SirLefti/piboy/docs/piboy.jpg

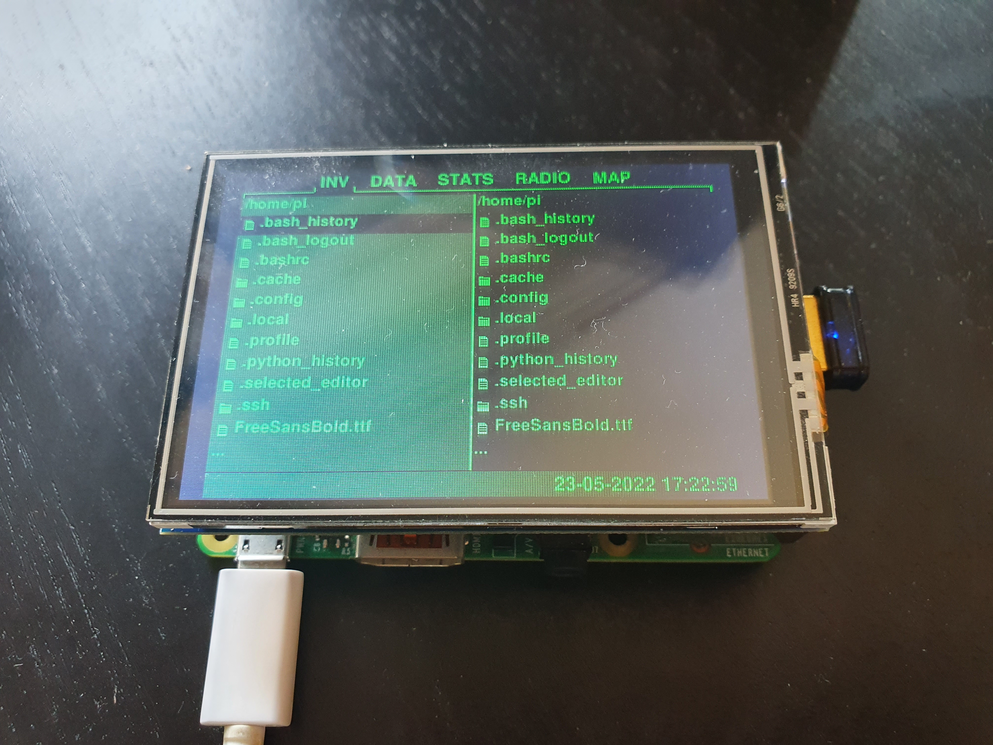
docs/piboy.jpg
