SirLefti/piboy/app/MapApp.py

import math
from typing import Any, Callable, Generator, Optional, Union

from injector import inject
from PIL import Image, ImageDraw, ImageOps

from app.App import SelfUpdatingApp
from core import resources
from core.decorator import override
from data.LocationProvider import Location, LocationException, LocationProvider
from data.TileProvider import TileProvider
from environment import AppConfig


class MapApp(SelfUpdatingApp):
    __SCROLL_FACTOR = 10
    __CONTROL_SIZE = 30
    __CONTROL_PADDING = 4

    class Control:
        """
        Represents a UI control element. A control has a texture, initial selection state, various callbacks and a flag
        that indicates, if it is an instant action. Instant actions will not get the SELECTED state when selected and
        thus cannot use callbacks the directional callbacks (up, right, down, left).
        """

        # not an enum, because we have to reassign the values
        class SelectionState:
            """
            Container class representing a state of a control element. A selection state has an element color and
            a background color.
            Initially, the state members are all none, replace them before usage or create new ones for a specific use.
            """

            # skip first argument, it is the value for the enum
            def __init__(self, color: tuple[int, int, int], background_color: tuple[int, int, int]):
                self.__color = color
                self.__background_color = background_color

            @property
            def color(self) -> tuple[int, int, int]:
                return self.__color

            @property
            def background_color(self) -> tuple[int, int, int]:
                return self.__background_color

        NONE: SelectionState
        FOCUSED: SelectionState
        SELECTED: SelectionState

        def __init__(self, icon_bitmap: Image.Image, initial_state: SelectionState,
                     on_select: Optional[Callable[[], None]] = None, on_deselect: Optional[Callable[[], None]] = None,
                     on_key_left: Optional[Callable[[], None]] = None,
                     on_key_right: Optional[Callable[[], None]] = None,
                     on_key_up: Optional[Callable[[], None]] = None, on_key_down: Optional[Callable[[], None]] = None,
                     instant_action=False):
            self.__icon_bitmap = icon_bitmap
            self.__on_select = on_select
            self.__on_deselect = on_deselect
            self.__on_key_left = on_key_left
            self.__on_key_right = on_key_right
            self.__on_key_up = on_key_up
            self.__on_key_down = on_key_down
            self.__instant_action = instant_action  # instant actions won't get the SELECTED flag
            self.__selection_state = initial_state

        def on_key_left(self):
            if self.__on_key_left is not None:
                self.__on_key_left()

        def on_key_right(self):
            if self.__on_key_right is not None:
                self.__on_key_right()

        def on_key_up(self):
            if self.__on_key_up is not None:
                self.__on_key_up()

        def on_key_down(self):
            if self.__on_key_down is not None:
                self.__on_key_down()

        def on_select(self):
            """When pressing button A"""
            if not self.__instant_action:
                self.__selection_state = self.SELECTED
            if self.__on_select is not None:
                self.__on_select()

        def on_deselect(self):
            """When pressing button B"""
            if not self.__instant_action:
                self.__selection_state = self.FOCUSED
            if self.__on_deselect is not None:
                self.__on_deselect()

        def on_focus(self):
            """When moving focus on this control"""
            self.__selection_state = self.FOCUSED

        def on_blur(self):
            """When moving focus away from this control"""
            self.__selection_state = self.NONE

        def draw(self, draw: ImageDraw.ImageDraw, left_top: tuple[int, int]):
            width, height = self.__icon_bitmap.size
            left, top = left_top
            draw.rectangle(left_top + (left + width - 1, top + height - 1),
                           fill=self.__selection_state.background_color)
            draw.bitmap(left_top, self.__icon_bitmap, fill=self.__selection_state.color)

        def is_selected(self) -> bool:
            return self.__selection_state == self.SELECTED

    @inject
    def __init__(self, draw_callback: Callable[[bool], None],
                 location_provider: LocationProvider, tile_provider: TileProvider, app_config: AppConfig):
        super().__init__(self.__update_location)
        self.__app_size = app_config.app_size
        self.__background = app_config.background
        self.__color = app_config.accent
        self.__color_dark = app_config.accent_dark
        self.__font = app_config.font_standard

        # init selection states
        self.Control.NONE = self.Control.SelectionState(self.__color_dark, self.__background)
        self.Control.FOCUSED = self.Control.SelectionState(self.__color, self.__background)
        self.Control.SELECTED = self.Control.SelectionState(self.__background, self.__color)

        self.__draw_callback = draw_callback
        self.__draw_callback_kwargs = {'partial': True}
        self.__location_provider = location_provider
        self.__tile_provider = tile_provider
        self.__zoom = 15
        self.__x_offset = 0
        self.__y_offset = 0
        self.__position: Union[Location, None] = None
        try:
            self.__position = self.__location_provider.get_location()
            self.__connection_lost = False
        except LocationException:
            self.__connection_lost = True

        def zoom_in():
            if self.__zoom + 1 in self.__tile_provider.zoom_range:
                self.__zoom = self.__zoom + 1

        def zoom_out():
            if self.__zoom - 1 in self.__tile_provider.zoom_range:
                self.__zoom = self.__zoom - 1

        def reset_offset():
            self.__x_offset = 0
            self.__y_offset = 0

        def move_left():
            self.__x_offset -= 1

        def move_right():
            self.__x_offset += 1

        def move_up():
            self.__y_offset -= 1

        def move_down():
            self.__y_offset += 1

        self.__controls: list[MapApp.Control] = [
            self.Control(ImageOps.invert(resources.minus_icon), initial_state=self.Control.NONE,
                         on_select=zoom_out, instant_action=True),
            self.Control(ImageOps.invert(resources.plus_icon), initial_state=self.Control.NONE,
                         on_select=zoom_in, instant_action=True),
            self.Control(ImageOps.invert(resources.move_icon), initial_state=self.Control.NONE,
                         on_key_left=move_left, on_key_right=move_right,
                         on_key_up=move_up, on_key_down=move_down,
                         on_select=self.stop_updating, on_deselect=self.start_updating),
            self.Control(ImageOps.invert(resources.focus_icon), initial_state=self.Control.NONE,
                         on_select=reset_offset, instant_action=True)
        ]
        self.__focused_control_index = 0
        # focus the currently focused control to initially update the selection state
        self.__controls[self.__focused_control_index].on_focus()

    @property
    @override
    def title(self) -> str:
        return 'MAP'

    @property
    @override
    def refresh_time(self) -> float:
        return 2.0

    def __update_location(self):
        if self.__x_offset == 0 and self.__y_offset == 0:
            try:
                self.__position = self.__location_provider.get_location()
                self.__connection_lost = False
            except LocationException:
                self.__connection_lost = True
            self.__draw_callback(**self.__draw_callback_kwargs)

    @override
    def draw(self, image: Image.Image, partial=False) -> Generator[tuple[Image.Image, int, int], Any, None]:
        draw = ImageDraw.Draw(image)
        width, height = self.__app_size
        left_top = (0, 0)
        side_tab_width = 120
        side_tab_padding = 5
        line_height = 20
        font = self.__font

        size = (width - side_tab_width, height)

        lat: Union[float, None] = None
        lon: Union[float, None] = None
        if self.__position is None:
            # if location is not available, just paste a black image for now
            left, top = left_top
            tile_width, tile_height = size
            right_bottom = (left + tile_width, top + tile_height)
            draw.rectangle(left_top + right_bottom, self.__background, self.__color, 3)
        else:
            # if location is available, just fetch the tile as usual
            lat = self.__position.latitude
            lon = self.__position.longitude
            tile = self.__tile_provider.get_tile(lat, lon, self.__zoom, size=size,
                                                 x_offset=self.__x_offset * self.__SCROLL_FACTOR,
                                                 y_offset=self.__y_offset * self.__SCROLL_FACTOR)
            image.paste(tile.image, left_top)

            # Calculate the relative position of the current location on the tile, because the tile is not centered
            # around the given location. It even works with resized and cropped tiles, as long as the center stays the
            # center. Otherwise, calculate the position where a virtual line from the center to the marker would cross
            # the edge to draw a different marker that indicates where the location would be.
            if self.__x_offset * self.__SCROLL_FACTOR + int(size[0] / 2) in range(size[0]) \
                    and self.__y_offset * self.__SCROLL_FACTOR + int(size[1] / 2) in range(size[1]):
                tile_top, tile_left = tile.top_left
                tile_bottom, tile_right = tile.bottom_right
                x_position = (lon - tile_left) / (tile_right - tile_left)
                y_position = (lat - tile_top) / (tile_bottom - tile_top)
                marker_center = (left_top[0] + size[0] * x_position - self.__x_offset * self.__SCROLL_FACTOR,
                                 left_top[1] + size[1] * y_position - self.__y_offset * self.__SCROLL_FACTOR)
                marker_size = 20
                draw.polygon([marker_center,
                              (marker_center[0] - int(marker_size / 2), marker_center[1] - marker_size),
                              (marker_center[0] + int(marker_size / 2), marker_center[1] - marker_size)],
                             fill=self.__color_dark)
            else:
                def draw_outside_marker(edge_position: tuple[int, int], center_position: tuple[int, int]):
                    marker_width = 3
                    marker_length_percentage = .2
                    tip_length_percentage = marker_length_percentage * .75
                    tip_angle = 30
                    diff_x = edge_position[0] - center_position[0]
                    diff_y = edge_position[1] - center_position[1]
                    draw.line((edge_position[0] - diff_x * marker_length_percentage,
                               edge_position[1] - diff_y * marker_length_percentage) +
                              edge_position, fill=self.__color, width=marker_width)  # line towards center

                    def dot(v1: tuple[float, float], v2: tuple[float, float]) -> float:
                        """ vector dot product """
                        return sum([i * j for (i, j) in zip(v1, v2)])

                    def mag(v: tuple[float, float]) -> float:
                        """ vector magnitude/length """
                        return math.sqrt(dot(v, v))

                    v_diff = (diff_x, diff_y)  # line vector with reference point at (0, 0)
                    v_ref = (0, 1)  # vector that goes straight up or down
                    adjust_left = 1 if v_diff[0] > v_ref[0] else -1  # adjust the angle if located left from ref point
                    dot_prod = dot(v_diff, v_ref)
                    mag_diff = mag(v_diff)
                    mag_ref = mag(v_ref)
                    radians = math.acos(dot_prod / (mag_diff * mag_ref))  # calculate angle in radians
                    angle = math.degrees(radians) * adjust_left  # convert to angle and adjust

                    tip_length = mag_diff * tip_length_percentage
                    # add 180 to flip and apply tip angle, convert back to radians
                    tip_1_x = tip_length * math.sin(math.radians(angle + tip_angle + 180))
                    tip_1_y = tip_length * math.cos(math.radians(angle + tip_angle + 180))
                    tip_2_x = tip_length * math.sin(math.radians(angle - tip_angle + 180))
                    tip_2_y = tip_length * math.cos(math.radians(angle - tip_angle + 180))

                    draw.line((edge_position[0] + tip_1_x, edge_position[1] + tip_1_y) +
                              edge_position, fill=self.__color, width=marker_width)  # first tip
                    draw.line((edge_position[0] + tip_2_x, edge_position[1] + tip_2_y) +
                              edge_position, fill=self.__color, width=marker_width)  # second tip

                # exclude cases where x_offset or y_offset are zero, division is not possible, but marker is straight
                # anyway
                map_center = (left_top[0] + size[0] // 2, left_top[1] + size[1] // 2)
                if self.__x_offset == 0:
                    if self.__y_offset > 0:
                        edge_center = (left_top[0] + size[0] // 2, left_top[1])
                        draw_outside_marker(edge_center, map_center)
                    else:
                        edge_center = (left_top[0] + size[0] // 2, left_top[1] + size[1])
                        draw_outside_marker(edge_center, map_center)
                elif self.__y_offset == 0:
                    if self.__x_offset > 0:
                        edge_center = (left_top[0], left_top[1] + size[1] // 2)
                        draw_outside_marker(edge_center, map_center)
                    else:
                        edge_center = (left_top[0] + size[0], left_top[1] + size[1] // 2)
                        draw_outside_marker(edge_center, map_center)
                else:
                    # neither x nor y are zero, division possible
                    # positive ratio means top-left or bottom-right sector, negativ means others
                    vertical_limit = size[0] / size[1]  # x / y
                    horizontal_limit = size[1] / size[0]  # y / x
                    vertical_ratio = self.__x_offset / self.__y_offset
                    horizontal_ratio = self.__y_offset / self.__x_offset
                    # calculate edge_center by taking the center of the edge and adding or subtracting the product of
                    # the other edge's half-length and the ratio
                    if -vertical_limit <= vertical_ratio <= vertical_limit:
                        if self.__y_offset > 0:
                            edge_center = (int(left_top[0] + size[0] // 2 - (size[1] // 2) * vertical_ratio),
                                           left_top[1])
                            draw_outside_marker(edge_center, map_center)
                        else:
                            edge_center = (int(left_top[0] + size[0] // 2 + (size[1] // 2) * vertical_ratio),
                                           left_top[1] + size[1])
                            draw_outside_marker(edge_center, map_center)
                    elif -horizontal_limit <= horizontal_ratio <= horizontal_limit:
                        if self.__x_offset > 0:
                            edge_center = (left_top[0],
                                           int(left_top[1] + size[1] // 2 - (size[0] // 2) * horizontal_ratio))
                            draw_outside_marker(edge_center, map_center)
                        else:
                            edge_center = (left_top[0] + size[0],
                                           int(left_top[1] + size[1] // 2 + (size[0] // 2) * horizontal_ratio))
                            draw_outside_marker(edge_center, map_center)

        # draw location info
        cursor = (left_top[0] + size[0] + side_tab_padding, left_top[1])
        draw.text(cursor, 'lat: unknown' if lat is None else 'lat: {:.4f}°'.format(lat), self.__color, font=font)
        cursor = (cursor[0], cursor[1] + line_height)
        draw.text(cursor, 'lon: unknown' if lon is None else 'lon: {:.4f}°'.format(lon), self.__color, font=font)
        cursor = (cursor[0], cursor[1] + line_height)
        draw.text(cursor, f'zoom: {self.__zoom}x', self.__color, font=font)
        if self.__x_offset != 0 or self.__y_offset != 0:
            cursor = (cursor[0], cursor[1] + line_height)
            draw.text(cursor, f'x: {self.__x_offset}, y: {self.__y_offset}', self.__color, font=font)
        if self.__connection_lost:
            cursor = (cursor[0], cursor[1] + line_height)
            draw.text(cursor, f'connection lost', self.__color, font=font)

        # draw controls
        cursor = (left_top[0] + size[0] - self.__CONTROL_SIZE - self.__CONTROL_PADDING,
                  left_top[1] + size[1] - self.__CONTROL_SIZE - self.__CONTROL_PADDING)
        for control in self.__controls:
            control.draw(draw, cursor)
            cursor = (cursor[0], cursor[1] - self.__CONTROL_SIZE - 2 * self.__CONTROL_PADDING)

        if partial:
            right_bottom = width, height
            yield image.crop(left_top + right_bottom), *left_top  # noqa (unpacking type check fail)
        else:
            yield image, 0, 0

    @override
    def on_key_left(self):
        if self.__controls[self.__focused_control_index].is_selected():
            self.__controls[self.__focused_control_index].on_key_left()

    @override
    def on_key_right(self):
        if self.__controls[self.__focused_control_index].is_selected():
            self.__controls[self.__focused_control_index].on_key_right()

    @override
    def on_key_up(self):
        if self.__controls[self.__focused_control_index].is_selected():
            self.__controls[self.__focused_control_index].on_key_up()
        else:
            self.__controls[self.__focused_control_index].on_blur()
            self.__focused_control_index = min(self.__focused_control_index + 1, len(self.__controls) - 1)
            self.__controls[self.__focused_control_index].on_focus()

    @override
    def on_key_down(self):
        if self.__controls[self.__focused_control_index].is_selected():
            self.__controls[self.__focused_control_index].on_key_down()
        else:
            self.__controls[self.__focused_control_index].on_blur()
            self.__focused_control_index = max(self.__focused_control_index - 1, 0)
            self.__controls[self.__focused_control_index].on_focus()

    @override
    def on_key_a(self):
        self.__controls[self.__focused_control_index].on_select()

    @override
    def on_key_b(self):
        self.__controls[self.__focused_control_index].on_deselect()
