SirLefti/piboy/app/UpdateApp.py

import logging
import re
import sys
import threading
from subprocess import CompletedProcess, run
from typing import Any, Callable, Collection, Generator, Optional

from injector import inject
from PIL import Image, ImageDraw

from app.App import App
from core.decorator import override
from environment import AppConfig

# type aliases
ActionCallable = Callable[[], CompletedProcess[str]]
ResultTextCallable = Callable[[CompletedProcess[str]], str]
ContinueCallable = Callable[[CompletedProcess[str]], bool]
ActionDefinition = tuple[ActionCallable, ResultTextCallable] | tuple[ActionCallable, ResultTextCallable, ContinueCallable]

logger = logging.getLogger('app')

class UpdateApp(App):
    LINE_HEIGHT = 20
    CENTER_OFFSET = 10

    class Option:

        def __init__(self, name: str, *actions: ActionDefinition):
            self._name = name
            self._actions = actions

        @property
        def name(self) -> str:
            return self._name

        @property
        def actions(self) -> Collection[ActionDefinition]:
            return self._actions

    class OptionWithCount(Option):

        def __init__(self, name: str, *actions: ActionDefinition, count_action: Callable[[], Optional[int]], count_name: str):
            super().__init__(name, *actions)
            self._count_action = count_action
            self._count_name = count_name

        @property
        @override
        def name(self) -> str:
            count = self._count_action()
            if count is not None:
                return f'{self._name} ({count} {self._count_name})'
            else:
                return f'{self._name} (error)'

        @property
        def count_action(self) -> Optional[Callable[[], Optional[int]]]:
            return self._count_action

        @property
        def count_name(self) -> Optional[str]:
            return self._count_name

    @inject
    def __init__(self, draw_callback: Callable[[bool], None], app_config: AppConfig):
        self.__draw_callback = draw_callback
        self.__app_size = app_config.app_size
        self.__background = app_config.background
        self.__color = app_config.accent
        self.__color_dark = app_config.accent_dark
        self.__app_top_offset = app_config.app_top_offset
        self.__app_side_offset = app_config.app_side_offset
        self.__app_bottom_offset = app_config.app_bottom_offset
        self.__font = app_config.font_standard

        self.__action_pending = False
        self.__selected_index = 0
        self.__files_to_reset: Optional[int] = None
        self.__files_to_clean: Optional[int] = None
        self.__commits_to_update: Optional[int] = None
        self.__branch_name = self.__get_branch_name()
        self.__remote_name = self.__get_remote_name()

        def get_files_to_reset() -> Optional[int]:
            return self.__files_to_reset

        def get_files_to_clean() -> Optional[int]:
            return self.__files_to_clean

        def get_commits_to_update() -> Optional[int]:
            return self.__commits_to_update

        def result_text_fetch(result: CompletedProcess[str]) -> str:
            if result.returncode != 0:
                return 'error fetching updates'
            if not result.stdout:
                return 'no updates available'
            return 'fetched updates, install next'

        def result_text_reset(result: CompletedProcess[str]) -> str:
            if result.returncode != 0:
                return 'error resetting changes'
            if not result.stdout:
                return 'no changes to reset'
            return 'reset changes'

        def result_text_clean(result: CompletedProcess[str]) -> str:
            if result.returncode != 0:
                return 'error cleaning files'
            if not result.stdout:
                return 'no files to clean'
            return 'cleaned files'

        def result_text_install(result: CompletedProcess[str]) -> str:
            if result.returncode != 0:
                return 'error installing updates'
            if result.stdout.count('\n') == 1:
                # has only one line break at the end if the message is 'already up to date', but more when updating
                return 'no updates to install'
            requirements_file_check = re.compile(r'requirements.*\.txt')
            if any(requirements_file_check.search(line) for line in result.stdout.split('\n')):
                return 'updates installed, wait for libs'
            return 'updates installed, restart next'

        def result_text_install_dependencies(result: CompletedProcess[str]) -> str:
            if result.returncode != 0:
                return 'error installing lib updates'
            if result.stdout.count('Successfully installed') == 0:
                return 'no lib updates to install, restart next'
            return 'lib updates installed, restart next'

        def result_text_shutdown(result: CompletedProcess[str]) -> str:
            if result.returncode != 0:
                return 'error shutting down'
            else:
                return 'shutting down...'

        def result_text_restart(result: CompletedProcess[str]) -> str:
            if result.returncode != 0:
                return 'error restarting'
            return 'restarting...'

        def continue_if_requirements_changed(result: CompletedProcess[str]) -> bool:
            if result.returncode != 0:
                return False
            requirements_file_check = re.compile(r'requirements.*\.txt')
            return any(requirements_file_check.search(line) for line in result.stdout.split('\n'))

        self.__options = [
            self.OptionWithCount('reset changes', (self.__run_reset, result_text_reset),
                                 count_action=get_files_to_reset, count_name='files'),
            self.OptionWithCount('clean files', (self.__run_clean, result_text_clean),
                                 count_action=get_files_to_clean, count_name='files'),
            self.Option('fetch updates', (self.__run_fetch, result_text_fetch)),
            self.OptionWithCount('install updates',
                                 (self.__run_install, result_text_install, continue_if_requirements_changed),
                                 (self.__run_install_dependencies, result_text_install_dependencies),
                                 count_action=get_commits_to_update, count_name='commits'),
            self.Option('shutdown', (self.__run_shutdown, result_text_shutdown)),
            self.Option('restart', (self.__run_restart, result_text_restart))
        ]
        self.__results: list[str] = []
        self.__last_results_length = len(self.__results)

    @staticmethod
    def __run_fetch() -> CompletedProcess[str]:
        # git fetch does not return stuff into stdout, return output of git log instead
        result = run(['git', 'fetch'], capture_output=True, text=True)
        if result.returncode != 0:
            return result
        return run(['git', 'log', '..@{u}', '--pretty=oneline'], capture_output=True, text=True)

    @staticmethod
    def __run_reset() -> CompletedProcess[str]:
        return run(['git', 'reset', '--hard'], capture_output=True, text=True)

    @staticmethod
    def __run_clean() -> CompletedProcess[str]:
        return run(['git', 'clean', '-fd'], capture_output=True, text=True)

    @staticmethod
    def __run_install() -> CompletedProcess[str]:
        return run(['git', 'pull'], capture_output=True, text=True)

    @staticmethod
    def __run_install_dependencies() -> CompletedProcess[str]:
        return run([sys.executable, '-m', 'pip', 'install', '-r', 'requirements-pi.txt'], capture_output=True, text=True)

    @staticmethod
    def __run_shutdown() -> CompletedProcess[str]:
        return run(['sudo', 'shutdown', 'now'], text=True)

    @staticmethod
    def __run_restart() -> CompletedProcess[str]:
        return run(['sudo', 'reboot', 'now'], text=True)

    @staticmethod
    def __get_files_to_reset() -> Optional[int]:
        result = run(['git', 'diff', '--name-only'], capture_output=True, text=True)
        if result.returncode != 0:
            return None
        if result.stdout is not None:
            return result.stdout.count('\n')
        return 0

    @staticmethod
    def __get_files_to_clean() -> Optional[int]:
        result = run(['git', 'clean', '-nd'], capture_output=True, text=True)
        if result.returncode != 0:
            return None
        if result.stdout is not None:
            return result.stdout.count('\n')
        return 0

    @staticmethod
    def __get_commits_to_update() -> Optional[int]:
        result = run(['git', 'rev-list', '@{upstream}', '--not', 'HEAD'], capture_output=True, text=True)
        if result.returncode != 0:
            return None
        if result.stdout is not None:
            return result.stdout.count('\n')
        return 0

    @staticmethod
    def __get_branch_name() -> Optional[str]:
        result = run(['git', 'branch', '--show-current'], capture_output=True, text=True)
        if result.returncode != 0:
            return None
        if result.stdout is not None:
            return result.stdout
        return None

    @staticmethod
    def __get_remote_name() -> Optional[str]:
        result = run(['git', 'remote', 'show'], capture_output=True, text=True)
        if result.returncode != 0:
            return None
        if result.stdout is not None:
            return result.stdout
        return None

    def __update_counts(self):
        self.__files_to_reset = self.__get_files_to_reset()
        self.__files_to_clean = self.__get_files_to_clean()
        self.__commits_to_update = self.__get_commits_to_update()

    @property
    @override
    def title(self) -> str:
        return 'SYS'

    @override
    def draw(self, image: Image.Image, partial=False) -> Generator[tuple[Image.Image, int, int], Any, None]:
        width, height = self.__app_size
        font = self.__font

        left_top = (0, 0)
        right_bottom = (width // 2, 0)
        draw = ImageDraw.Draw(image)

        # part: result history
        if self.__last_results_length != len(self.__results) or not partial:
            self.__last_results_length = len(self.__results)

            # clear existing logs
            history_cursor: tuple[int, int] = (width // 2 + self.CENTER_OFFSET, left_top[1])
            rect_right_bottom = (width, history_cursor[1] + min(len(self.__results) * self.LINE_HEIGHT, height))
            draw.rectangle(history_cursor + rect_right_bottom, fill=self.__background)
            # and draw history in reverse order
            for text in reversed(self.__results):
                _, _, _, text_height = font.getbbox(text)
                if history_cursor[1] + text_height > height:
                    break
                draw.text(history_cursor, text, fill=self.__color, font=font)
                history_cursor = (history_cursor[0], history_cursor[1] + self.LINE_HEIGHT)
            right_bottom = (width, history_cursor[1])

        # part: options
        cursor: tuple[int, int] = left_top
        for index, option in enumerate(self.__options):
            if index == self.__selected_index:
                draw.rectangle(cursor + (width // 2, cursor[1] + self.LINE_HEIGHT), fill=self.__color_dark)
            else:
                draw.rectangle(cursor + (width // 2, cursor[1] + self.LINE_HEIGHT), fill=self.__background)
            text = option.name
            draw.text(cursor, text, fill=self.__color, font=font)
            cursor = (cursor[0], cursor[1] + self.LINE_HEIGHT)
            right_bottom = (max(right_bottom[0], width // 2), max(right_bottom[1], cursor[1]))
        draw.line((width // 2, left_top[1]) + (width // 2, height), fill=self.__color, width=1)

        # part: repository and branch information
        unknown = 'unknown'
        _, _, _, text_height_branch = font.getbbox(self.__branch_name or unknown)
        _, _, _, text_height_remote = font.getbbox(self.__remote_name or unknown)
        draw.text((0, height - text_height_branch -
                   text_height_remote), f'branch: {self.__branch_name or unknown}', fill=self.__color, font=font)
        draw.text((0, height - text_height_remote),
                  f'remote: {self.__remote_name or unknown}', fill=self.__color, font=font)

        if partial:
            yield image.crop(left_top + right_bottom), *left_top  # noqa (unpacking type check fail)
        else:
            yield image, 0, 0

    @override
    def on_key_up(self):
        self.__selected_index = (self.__selected_index - 1) % len(self.__options)

    @override
    def on_key_down(self):
        self.__selected_index = (self.__selected_index + 1) % len(self.__options)

    @override
    def on_key_a(self):
        if self.__action_pending:
            self.__results.append('action pending')
            self.__draw_callback(True)
        else:
            def process_all():
                option = self.__options[self.__selected_index]
                self.__action_pending = True
                for action_definition in option.actions:
                    action_callable, result_text_callable, continue_callable \
                        = action_definition if len(action_definition) == 3 else (*action_definition, None)
                    result = action_callable()
                    # Log complete output
                    if result.stdout:
                        logger.info(result.stdout.rstrip('\n'))
                    if result.stderr:
                        logger.error(result.stderr.rstrip('\n'))
                    self.__results.append(result_text_callable(result))
                    self.__update_counts()
                    self.__draw_callback(True)
                    if continue_callable is not None:
                        if not continue_callable(result):
                            break
                self.__action_pending = False

            thread = threading.Thread(target=process_all, args=(), daemon=True)
            thread.start()

    @override
    def on_app_enter(self):
        self.__update_counts()
