SirLefti/piboy/data/OSMTileProvider.py

import io
import logging
import math
import os
import threading
import time
from functools import lru_cache
from typing import Iterable

import requests
from PIL import Image, ImageDraw, ImageFont, UnidentifiedImageError
from requests.exceptions import ConnectionError, RequestException

from core.decorator import override
from data.TileProvider import TileInfo, TileProvider

logger = logging.getLogger('tile_data')

class TileNotReadyError(Exception):
    """Raised when a file has not been fetched yet, which runs in the background, and will be available soon"""


class OSMTileProvider(TileProvider):

    __CACHE_DURATION = 1000 * 60 * 60 * 24 * 365  # one year in ms
    __OSM_TILE_SIZE = (256, 256)  # size of a tile image from OSM
    __LRU_CACHE_SIZE = 16
    __TILE_CACHE_PATH = '.tiles'
    __TILE_CACHE_TEMPLATE = '{zoom}-{x}-{y}.png'
    __PENDING_TILES: set[tuple[int, int, int]] = set()
    __PENDING_LOCK = threading.Lock()

    def __init__(self, background: tuple[int, int, int], color: tuple[int, int, int], font: ImageFont.FreeTypeFont):
        self.__background = background
        self.__color = color
        self.__font = font

    @property
    @override
    def zoom_range(self) -> Iterable[int]:
        return range(0, 20)

    @override
    def get_tile(self, lat: float, lon: float, zoom: int, size: tuple[int, int] = (256, 256), x_offset: int = 0,
                 y_offset: int = 0) -> TileInfo:
        x_tile, y_tile = self._deg_to_num(lat, lon, zoom)
        tile: Image.Image
        try:
            tile = self._fetch_tile(zoom, x_tile, y_tile)
        except (ValueError, FileNotFoundError, ConnectionError, UnidentifiedImageError) as e:
            logger.warning(e)
            tile = self._get_placeholder_tile()
        except TileNotReadyError:
            tile = self._get_placeholder_tile()
        tile_width, tile_height = tile.size
        target_width, target_height = size

        # calculate the relative position of the current location on the tile, because the tile is not centered around
        # the given location.
        tile_top_deg, tile_left_deg = self._num_to_deg(x_tile, y_tile, zoom)
        tile_bottom_deg, tile_right_deg = self._num_to_deg(x_tile + 1, y_tile + 1, zoom)
        x_position = int((lon - tile_left_deg) / (tile_right_deg - tile_left_deg) * tile_width) + x_offset
        y_position = int((lat - tile_top_deg) / (tile_bottom_deg - tile_top_deg) * tile_height) + y_offset

        # calculate the total tiles to be fetched
        left_tiles = int((target_width / 2 - x_position + tile_width) / tile_width)
        right_tiles = int((target_width / 2 - (tile_width - x_position) + tile_width) / tile_width)
        top_tiles = int((target_height / 2 - y_position + tile_height) / tile_height)
        bottom_tiles = int((target_height / 2 - (tile_height - y_position) + tile_height) / tile_height)

        def generate_tile(x, y) -> Image.Image:
            if y_tile - top_tiles + y < 0 or y_tile - top_tiles + y == math.pow(2, zoom):
                # empty image if tile ends on top or bottom and there is no further tile
                return Image.new('RGB', size, self.__background)
            else:
                try:
                    return self._fetch_tile(zoom, (x_tile - left_tiles + x) % int(math.pow(2, zoom)),
                                                  (y_tile - top_tiles + y) % int(math.pow(2, zoom)))
                except (ValueError, FileNotFoundError, ConnectionError, UnidentifiedImageError) as ex:
                    logger.warning(ex)
                    return self._get_placeholder_tile()
                except TileNotReadyError:
                    return self._get_placeholder_tile()

        grid = [[generate_tile(x, y) for y in range(top_tiles + 1 + bottom_tiles)]
                for x in range(left_tiles + 1 + right_tiles)]

        merged_tile = Image.new('RGB', (len(grid) * tile_width, len(grid[0]) * tile_height), (255, 255, 255))
        for row_index, row in enumerate(grid):
            for patch_index, patch in enumerate(row):
                merged_tile.paste(patch, (row_index * tile_width, patch_index * tile_height))

        center_x = int(tile_width * left_tiles + x_position)
        center_y = int(tile_height * top_tiles + y_position)
        cropped_left = center_x - int(target_width / 2)
        cropped_top = center_y - int(target_height / 2)
        cropped_tile = merged_tile.crop((cropped_left, cropped_top,
                                         cropped_left + target_width, cropped_top + target_height))
        width_deg = (tile_right_deg - tile_left_deg) * (tile_width / target_width)
        height_deg = (tile_bottom_deg - tile_top_deg) * (tile_height / target_height)
        top_left = lat - (height_deg / 2), lon - (width_deg / 2)
        bottom_right = lat + (height_deg / 2), lon + (width_deg / 2)
        return TileInfo(top_left, bottom_right, cropped_tile)

    def _get_placeholder_tile(self) -> Image.Image:
        font = self.__font
        tile = Image.new('RGB', self.__OSM_TILE_SIZE, self.__background)
        text_w, text_h = font.getbbox('?')[-2:]
        tile_w, tile_h = tile.size
        draw = ImageDraw.Draw(tile)
        draw.rectangle((0, 0) + self.__OSM_TILE_SIZE, fill=self.__background, outline=self.__color, width=1)
        draw.text((tile_w / 2 - text_w / 2, tile_h / 2 - text_h / 2), '?', font=font)
        return tile

    @classmethod
    @lru_cache(__LRU_CACHE_SIZE)
    def _fetch_tile(cls, zoom: int, x_tile: int, y_tile: int) -> Image.Image:
        """Fetches the requested tile either from cache or from OSM tile API"""
        if not os.path.isdir(cls.__TILE_CACHE_PATH):
            os.mkdir(cls.__TILE_CACHE_PATH)
        tile_path = os.path.join(cls.__TILE_CACHE_PATH, cls.__TILE_CACHE_TEMPLATE.format(zoom=zoom, x=x_tile, y=y_tile))
        if os.path.isfile(tile_path) and time.time() - os.path.getmtime(tile_path) < cls.__CACHE_DURATION:
            with open(tile_path, 'rb') as f:
                logger.debug(f'loaded {zoom}-{x_tile}-{y_tile} from file cache')
                return Image.open(io.BytesIO(f.read()))
        key = (zoom, x_tile, y_tile)
        with cls.__PENDING_LOCK:
            already_fetching = key in cls.__PENDING_TILES
            cls.__PENDING_TILES.add(key)
        if not already_fetching:
            logger.debug(f'started fetch {zoom}-{x_tile}-{y_tile} from openstreetmaps')
            threading.Thread(target=cls._fetch_and_store_tile_background_task, args=key, daemon=True).start()
        raise TileNotReadyError(f'tile {zoom}-{x_tile}-{y_tile} is fetched in the background')

    @classmethod
    def _fetch_and_store_tile_background_task(cls, zoom: int, x_tile: int, y_tile: int):
        headers = {
            'User-Agent': 'piboy'
        }
        tile_path = os.path.join(cls.__TILE_CACHE_PATH, cls.__TILE_CACHE_TEMPLATE.format(zoom=zoom, x=x_tile, y=y_tile))
        try:
            response = requests.get(f'https://tile.openstreetmap.org/{zoom}/{x_tile}/{y_tile}.png', headers=headers)
            if response.status_code == 200:
                with open(tile_path, 'wb') as f:
                    logger.debug(f'fetched {zoom}-{x_tile}-{y_tile} from openstreetmaps')
                    f.write(response.content)
            else:
                logger.warning(f'Fetching OSM tile ({zoom}-{x_tile}-{y_tile}) failed ({response.status_code})')
        except RequestException as e:
            logger.warning(e)
        finally:
            with cls.__PENDING_LOCK:
                cls.__PENDING_TILES.discard((zoom, x_tile, y_tile))

    @classmethod
    def _deg_to_num(cls, lat_deg: float, lon_deg: float, zoom: int) -> tuple[int, int]:
        """Code from: https://wiki.openstreetmap.org/wiki/Slippy_map_tilenames"""
        lat_rad = math.radians(lat_deg)
        n = 2.0 ** zoom
        x_tile = int((lon_deg + 180.0) / 360.0 * n)
        y_tile = int((1.0 - math.asinh(math.tan(lat_rad)) / math.pi) / 2.0 * n)
        return x_tile, y_tile

    @classmethod
    def _num_to_deg(cls, x_tile: int, y_tile: int, zoom: int) -> tuple[float, float]:
        """Code from: https://wiki.openstreetmap.org/wiki/Slippy_map_tilenames"""
        n = 2.0 ** zoom
        lon_deg = x_tile / n * 360.0 - 180.0
        lat_rad = math.atan(math.sinh(math.pi * (1 - 2 * y_tile / n)))
        lat_deg = math.degrees(lat_rad)
        return lat_deg, lon_deg
