SirLefti/piboy/interaction/SelfManagedTkInteraction.py

import tkinter as tk
from typing import Callable

from PIL import Image, ImageTk

from core.decorator import override
from interaction.Display import Display
from interaction.Input import Input
from interaction.UnifiedInteraction import UnifiedInteraction


class SelfManagedTkInteraction(UnifiedInteraction):

    BUTTON_W = 15
    BUTTON_H = 6

    def __init__(self, on_key_left: Callable[[Display], None], on_key_right: Callable[[Display], None],
                 on_key_up: Callable[[Display], None], on_key_down: Callable[[Display], None],
                 on_key_a: Callable[[Display], None], on_key_b: Callable[[Display], None],
                 on_rotary_change: Callable[[Display, int], None],
                 on_rotary_switch: Callable[[Display], None],
                 resolution: tuple[int, int], background: tuple[int, int, int], ui_background: tuple[int, int, int]):
        Input.__init__(self, lambda: on_key_left(self), lambda: on_key_right(self),
                       lambda: on_key_up(self), lambda: on_key_down(self),
                       lambda: on_key_a(self), lambda: on_key_b(self),
                       lambda steps: on_rotary_change(self, steps),
                       lambda: on_rotary_switch(self))
        self.__resolution = resolution
        self.__background = background
        self.__image = Image.new('RGB', resolution, background)

        self.__root = tk.Tk()
        self.__root.title('PiBoy - Simulator')
        self.__root.configure(bg='#%02x%02x%02x' % ui_background)
        self.__image_tk = ImageTk.PhotoImage(self.__image)
        self.__label = tk.Label(self.__root, image=self.__image_tk)
        self.__label.grid(row=0, column=0, rowspan=4)

        button_left = tk.Button(self.__root, width=self.BUTTON_W, height=self.BUTTON_H, text='left',
                                command=self.on_key_left)
        button_left.grid(row=1, column=1)
        button_up = tk.Button(self.__root, width=self.BUTTON_W, height=self.BUTTON_H, text='up',
                              command=self.on_key_up)
        button_up.grid(row=0, column=2)
        button_right = tk.Button(self.__root, width=self.BUTTON_W, height=self.BUTTON_H, text='right',
                                 command=self.on_key_right)
        button_right.grid(row=1, column=3)
        button_down = tk.Button(self.__root, width=self.BUTTON_W, height=self.BUTTON_H, text='down',
                                command=self.on_key_down)
        button_down.grid(row=2, column=2)
        button_a = tk.Button(self.__root, width=self.BUTTON_W, height=self.BUTTON_H, text='button a',
                             command=self.on_key_a)
        button_a.grid(row=2, column=4)
        button_b = tk.Button(self.__root, width=self.BUTTON_W, height=self.BUTTON_H, text='button b',
                             command=self.on_key_b)
        button_b.grid(row=2, column=5)
        button_decrease = tk.Button(self.__root, width=self.BUTTON_W, height=self.BUTTON_H, text='-',
                                    command=lambda: self.on_rotary_change(-1))
        button_decrease.grid(row=0, column=4)
        button_increase = tk.Button(self.__root, width=self.BUTTON_W, height=self.BUTTON_H, text='+',
                                    command=lambda: self.on_rotary_change(1))
        button_increase.grid(row=0, column=5)

    @override
    def show(self, image: Image.Image, x0: int, y0: int):
        self.__image.paste(image, (x0, y0))
        self.__image_tk = ImageTk.PhotoImage(self.__image)
        self.__label.configure(image=self.__image_tk)

    @override
    def close(self):
        pass

    def run(self):
        """blocking function to actually run the UI"""
        self.__root.mainloop()
