SirLefti/piboy/app/EnvironmentApp.py

from typing import Any, Callable, Generator

from injector import inject
from PIL import Image, ImageDraw

from app.App import SelfUpdatingApp
from core import resources
from core.decorator import override
from data.EnvironmentDataProvider import EnvironmentData, EnvironmentDataProvider
from environment import AppConfig


class EnvironmentApp(SelfUpdatingApp):

    @inject
    def __init__(self, draw_callback: Callable[[bool], None],
                 data_provider: EnvironmentDataProvider, app_config: AppConfig):
        super().__init__(self.__update_data)
        self.__app_size = app_config.app_size
        self.__background = app_config.background
        self.__color = app_config.accent
        self.__color_dark = app_config.accent_dark
        self.__font = app_config.font_standard

        self.__draw_callback = draw_callback
        self.__draw_callback_kwargs = {'partial': True}
        self.__data_provider = data_provider
        self.__data: EnvironmentData | None = None

        self.__data = self.__data_provider.get_environment_data()

        self.__t_icon = resources.temperature_icon
        self.__p_icon = resources.pressure_icon
        self.__h_icon = resources.humidity_icon

    @property
    @override
    def refresh_time(self) -> float:
        return 1

    @property
    @override
    def title(self) -> str:
        return 'ENV'

    def __update_data(self):
        self.__data = self.__data_provider.get_environment_data()
        self.__draw_callback(**self.__draw_callback_kwargs)

    @override
    def draw(self, image: Image.Image, partial=False) -> Generator[tuple[Image.Image, int, int], Any, None]:
        draw = ImageDraw.Draw(image)
        width, height = self.__app_size
        icon_gap = 10
        left_top = ((width - self.__t_icon.width - self.__p_icon.width - self.__h_icon.width - 2 * icon_gap) // 2, 50)

        temperature_xy = left_top
        pressure_xy = (temperature_xy[0] + self.__t_icon.width + icon_gap, temperature_xy[1])
        humidity_xy = (pressure_xy[0] + self.__p_icon.width + icon_gap, pressure_xy[1])

        # only drawn once
        if not partial:
            draw.bitmap(temperature_xy, self.__t_icon, fill=self.__color)
            draw.bitmap(pressure_xy, self.__p_icon, fill=self.__color)
            draw.bitmap(humidity_xy, self.__h_icon, fill=self.__color)

        draw_area_left_top = (left_top[0],
                              min(temperature_xy[1] + self.__t_icon.height,
                              pressure_xy[1] + self.__p_icon.height,
                              humidity_xy[1] + self.__h_icon.height))

        # format with two decimals, and seven characters in total (adds whitespaces on the left to fill)
        t_text = f'{self.__data.temperature:.2f} °C' if self.__data is not None else '? °C'
        p_text = f'{self.__data.pressure:.2f} hPa' if self.__data is not None else '? hPa'
        h_text = f'{self.__data.humidity:.2%}' if self.__data is not None else '?%'
        _, _, t_text_width, t_text_height = self.__font.getbbox(t_text)
        _, _, p_text_width, p_text_height = self.__font.getbbox(p_text)
        _, _, h_text_width, h_text_height = self.__font.getbbox(h_text)
        draw.text((temperature_xy[0] + (self.__t_icon.width - t_text_width) // 2,
                   temperature_xy[1] + self.__t_icon.height + icon_gap),
                  t_text, self.__color, font=self.__font)
        draw.text((pressure_xy[0] + (self.__p_icon.width - p_text_width) // 2,
                   pressure_xy[1] + self.__p_icon.height + icon_gap),
                  p_text, self.__color, font=self.__font)
        draw.text((humidity_xy[0] + (self.__h_icon.width - h_text_width) // 2,
                   humidity_xy[1] + self.__h_icon.height + icon_gap),
                  h_text, self.__color, font=self.__font)

        if partial:
            right_bottom = (humidity_xy[0] + (self.__h_icon.width - h_text_width) // 2 + h_text_width,
                            draw_area_left_top[1] + icon_gap + max(t_text_height, p_text_height, h_text_height))
            yield image.crop(draw_area_left_top + right_bottom), *draw_area_left_top  # noqa (unpacking type check fail)
        else:
            yield image, 0, 0
