SirLefti/piboy/data/BatteryStatusProvider.py

from abc import ABC, abstractmethod

from core.closeable import Closeable
from core.data import DeviceStatus


class BatteryStatusProvider(Closeable, ABC):
    """Data provider for the state of charge of the battery."""

    @abstractmethod
    def get_state_of_charge(self) -> float:
        """Returns state of charge as a float between 0 and 1."""
        raise NotImplementedError

    @abstractmethod
    def get_device_status(self) -> DeviceStatus:
        """Returns the device status of the hardware module."""
        raise NotImplementedError
