SirLefti/piboy/data/FakeBatteryStatusProvider.py

from core.data import DeviceStatus
from core.decorator import override
from data.BatteryStatusProvider import BatteryStatusProvider


class FakeBatteryStatusProvider(BatteryStatusProvider):
    @override
    def close(self):
        pass

    @override
    def get_state_of_charge(self) -> float:
        return 1.0

    @override
    def get_device_status(self) -> DeviceStatus:
        return DeviceStatus.OPERATIONAL
